and3rson/pk88/metalbios/src/keyboard.asm

; =====================================================
;
; Keyboard functions (GAL22V10)
; http://forum.6502.org/viewtopic.php?f=10&t=7833
;
; This file is part of MetalBIOS for PK-88.
;
; =====================================================

        cpu     8086
        bits    16

        %include "sys.inc"
        %include "ports.inc"
        %include "bda.inc"

        section .rodata

FLAG_BREAK      equ     0x01    ; Flag bits
FLAG_EXT        equ     0x02

MOD_SHIFT       equ     0x01    ; Modifier bits
MOD_CTRL        equ     0x02

LSHIFT          equ     0x12    ; Scan codes (set 2)
RSHIFT          equ     0x59

LCTRL           equ     0x14    ; Scan codes (set 2)
RCTRL           equ     0x114

CTL_BRK         equ     0x2E03  ; Scan code (set 1)

type    KEYMAP  object
KEYMAP:
        ; This basically maps scan codes that come from PS/2 keyboard (set 2) into BIOS scan codes (set 1).
        ; Basic codes
        ;               F9              F5      F3      F1      F2      F12                     F10     F8      F6      F4      TAB     `
        dw      0x0000, 0x4300, 0x0000, 0x3F00, 0x3D00, 0x3B00, 0x3C00, 0x8600,         0x0000, 0x4400, 0x4200, 0x4000, 0x3E00, 0x0F09, 0x2960, 0x0000
        ;               LALT    LSHIFT          LCTRL   Q       1                                       Z       S       A       W       2
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
        dw      0x0000, 0x0000, 0x0000, 0x0000, 0x0000, 0x0000, 0x0000, 0x0000,         0x0000, 0x0000, 0x0000, 0x0000, 0x0000, 0x0000, 0x0000, 0x0000
        dw      0x0000, 0x0000, 0x0000, 0x0000, 0x0000, 0x0000, 0x0000, 0x0000,         0x0000, 0x0000, 0x0000, 0x0000, 0x0000, 0x0000, 0x0000, 0x0000
        dw      0x0000, 0x0000, 0x0000, 0x0000, 0x0000, 0x0000, 0x0000, 0x0000,         0x0000, 0x0000, 0x0000, 0x0000, 0x0000, 0x0000, 0x0000, 0x0000

        section .text

; -----------------------------------------------------
; Initialize keyboard controller
; -----------------------------------------------------
        global  keyboard_init
keyboard_init:
        push    ax
        push    es

        ; Init keyboard buffers
        mov     ax, BDA_SEG
        mov     es, ax
        mov     word [es:BDA_KB_VALUE], 0
        mov     byte [es:BDA_KB_FLAGS], 0
        mov     byte [es:BDA_KB_MODS], 0

        ; Reset keyboard controller
        out     KB_RES, al

        pop     es
        pop     ax
        ret

; --------------------------------------------------
; Read & process PS/2 byte
; --------------------------------------------------
        global  keyboard_process
keyboard_process:
        push    ax
        push    bx
        push    ds
        push    es

        ; Read keyboard byte
        in      al, KB_DAT
        ; Reset keyboard controller
        out     KB_RES, al

        ; DS = BDA segment, ES = ROM segment
        mov     bx, BDA_SEG
        mov     ds, bx
        mov     bx, ROM_SEG
        mov     es, bx

        cmp     al, 0xAA        ; Is BAT code?
        jne     .not_bat
        jmp     .done           ; Ignore
.not_bat:
        cmp     al, 0xF0        ; Is break code marker?
        je      .set_break      ; Set break flag
        cmp     al, 0xE0        ; Is extended code marker?
        je      .set_ext        ; Set extended flag

        ; Load & clear flags
        mov     bl, [BDA_KB_FLAGS]
        mov     byte [BDA_KB_FLAGS], 0

        ; Convert 8-bit scan code to 16-bit, add 256 if extended flag is set
        xor     ah, ah
        test    bl, FLAG_EXT
        jz      .no_ext
        add     ax, 256
.no_ext:

        ; Is this a shift key?
        cmp     ax, LSHIFT
        je      .shift
        cmp     ax, RSHIFT
        je      .shift

        ; Is this a ctrl key?
        cmp     ax, LCTRL
        je      .ctrl
        cmp     ax, RCTRL
        je      .ctrl

        ; Is break flag set?
        test    bl, FLAG_BREAK
        jnz     .done

        ; Convert scan code to offset in key map
        mov     bx, ax
        shl     bx, 1

        ; Is ctrl modifier active?
        test    byte [BDA_KB_MODS], MOD_CTRL
        jnz     .ctrled
        ; Is shift modifier active?
        test    byte [BDA_KB_MODS], MOD_SHIFT
        jnz     .shifted
.normal:
        mov     ax, [es:KEYMAP + bx]
        jmp     .store
.ctrled:
        mov     ax, [es:KEYMAP_CTRLED + bx]
        ; Is this a ctrl-break?
        ; cmp     ax, CTL_BRK
        ; jne     .store
        ; int     0x1B            ; Call BIOS INT 1Bh handler
        jmp     .store
.shifted:
        mov     ax, [es:KEYMAP_SHIFTED + bx]
.store:
        ; Store key code in BDA
        mov     [BDA_KB_VALUE], ax

        jmp     .done

.set_break:
        ; Received break code marker
        or      byte [BDA_KB_FLAGS], FLAG_BREAK
        jmp     .done

.set_ext:
        ; Received extended code marker
        or      byte [BDA_KB_FLAGS], FLAG_EXT
        jmp     .done

.shift:
        test    bl, FLAG_BREAK
        jnz     .shift_released
.shift_pressed:
        ; Shift key pressed
        or      byte [BDA_KB_MODS], MOD_SHIFT
        jmp     .done
.shift_released:
        ; Shift key released
        and     byte [BDA_KB_MODS], ~MOD_SHIFT

.ctrl:
        test    bl, FLAG_BREAK
        jnz     .ctrl_released
.ctrl_pressed:
        ; Ctrl key pressed
        or      byte [BDA_KB_MODS], MOD_CTRL
        jmp     .done
.ctrl_released:
        ; Ctrl key released
        and     byte [BDA_KB_MODS], ~MOD_CTRL

.done:
        pop     es
        pop     ds
        pop     bx
        pop     ax

        ret
