and3rson/pk88/metalbios/src/int16h.asm

; =====================================================
;
; Keyboard functions (BIOS int 0x16)
;
; This file is part of MetalBIOS for PK-88.
;
; =====================================================

        cpu     8086
        bits    16

        %include "bda.inc"
        %include "sys.inc"
        %include "macros.inc"

        extern  lcd_write
        extern  lcd_busy
        extern  lcd_print
        extern  lcd_printbyte
        extern  lcd_printm

        section .rodata

type    STUB_S  object
STUB_S  db      "!0x16:", 0

        section .text

; --------------------------------------------------
; BIOS 0x16 ISR
; --------------------------------------------------
; Args:
;   AH - function number
        global  int16h_isr
int16h_isr:
        sti

        push    si
        push    bx  ; Save BX to perform pointer arithmetic

        mov     bl, ah
        xor     bh, bh  ; BX now contains function number

        ; Load int16h_function_table with BX*2 offset into BX
        shl     bx, 1
        mov     bx, [cs:bx+int16h_function_table]

        mov     si, bx
        pop     bx
        ; NOTE: SI will be clobbered in the called function
        call    si  ; Call appropriate function
        pop     si

        iretc

int16h_function_table:
        dw      wait_for_keypress  ; ELKS
        dw      peek_char  ; ELKS
        dw      int16h_nop
        dw      int16h_nop
        dw      int16h_nop
        dw      int16h_nop
        dw      int16h_nop
        dw      int16h_nop

; --------------------------------------------------
; No-op (unimplemented) function
; --------------------------------------------------
int16h_nop:
        push    bp
        push    es
        push    ax

        mov     ax, ROM_SEG
        mov     es, ax
        mov     ah, 0x13
        mov     bp, STUB_S
        int     0x10

        pop     ax
        xchg    ah, al
        call    lcd_printbyte
        xchg    ah, al
        pop     es
        pop     bp

        stc
        ret

; --------------------------------------------------
; Function 0x00 - Wait for keypress, halt until pressed
; --------------------------------------------------
; Returns:
;   AH - scan code
;   AL - ASCII character or zero if special key
wait_for_keypress:
        push    es

        mov     ax, BDA_SEG
        mov     es, ax

.wait:
        mov     ax, [es:BDA_KB_VALUE]
        test    ax, ax
        jz      .wait

        ; Clear scan code
        and     word [es:BDA_KB_VALUE], 0

        pop     es

        clc
        ret

; --------------------------------------------------
; Function 0x01 - Peek character from keyboard buffer
; --------------------------------------------------
; Returns:
;   ZF - 0 if a key is pressed (even Ctrl-Break)
;   AX - 0 if no scan code is available
;   AH - scan code
;   AL - ASCII character or zero if special function key
peek_char:
        push    bp
        mov     bp, sp
        ; Stack:
        ;   BP+0 - original BP
        ;   BP+2 - return address (inside int16h_isr)
        ;   BP+4 - SI (pushed at start of int16h_isr)
        ;   BP+6 - IP
        ;   BP+8 - CS
        ;   BP+10 - flags (ZF is bit 6)
        push    es

        mov     ax, BDA_SEG
        mov     es, ax

        mov     ax, [es:BDA_KB_VALUE]
        test    ax, ax
        jz      .no_key

.has_key:
        ; Clear zero flag in BP+10
        and     byte [bp+10], 0xBF
        jmp     .done

.no_key:
        ; Set zero flag in BP+10
        or      byte [bp+10], 0x40

.done:
        pop     es
        pop     bp

        clc
        ret
